DynAis/duino-access/doc/XM-04-HID蓝牙HID模块/JX-04-HID-M 解决方案.png

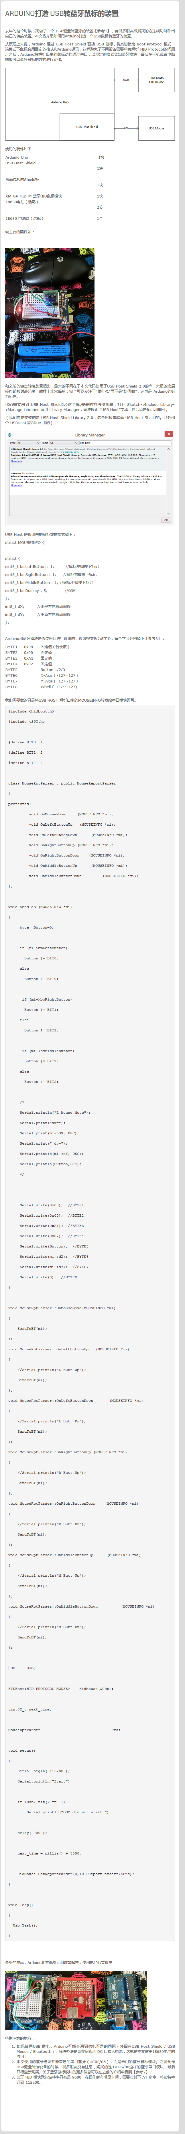
doc/XM-04-HID蓝牙HID模块/JX-04-HID-M 解决方案.png
