DynAis/duino-access/include/DAstate.h

//在这个文件里添加mian.cpp运行的状态
#define DA_STATE_PRESSTEST                  0
#define DA_STATE_ENROLL                     1
#define DA_STATE_DETECT                     2
#define DA_STATE_GETINFO                    3
#define DA_STATE_CLEAR                      4
#define DA_STATE_SETPARAM                   5
